raviaw/roundtftmonitor/stand/views/fit-dark.png

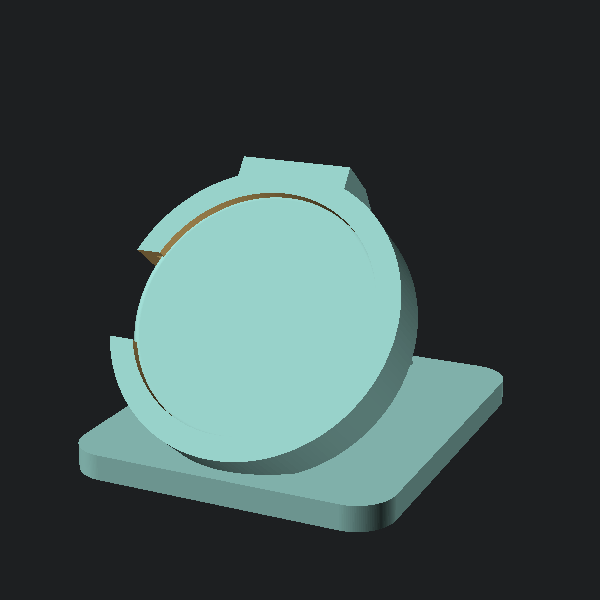
stand/views/fit-dark.png
