raviaw/roundtftmonitor/stand/views/fit-light.png

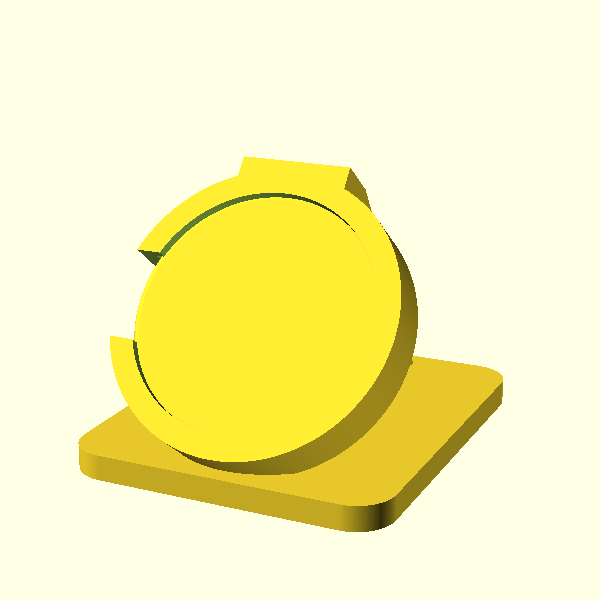
stand/views/fit-light.png
