raviaw/roundtftmonitor/stand/views/iso-dark.png

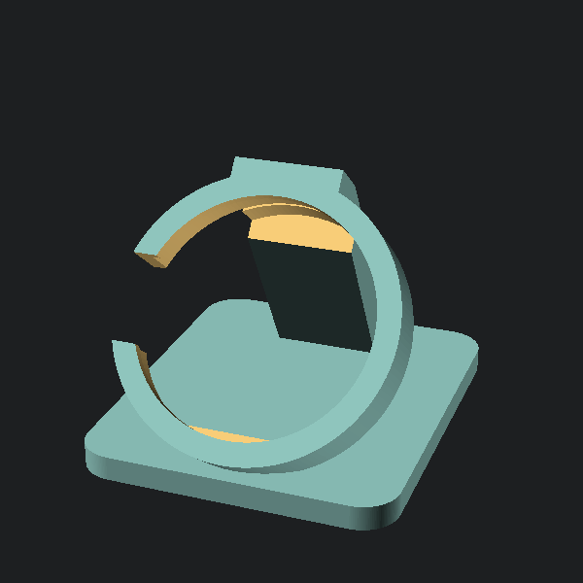
stand/views/iso-dark.png
