raviaw/roundtftmonitor/stand/views/top-light.png

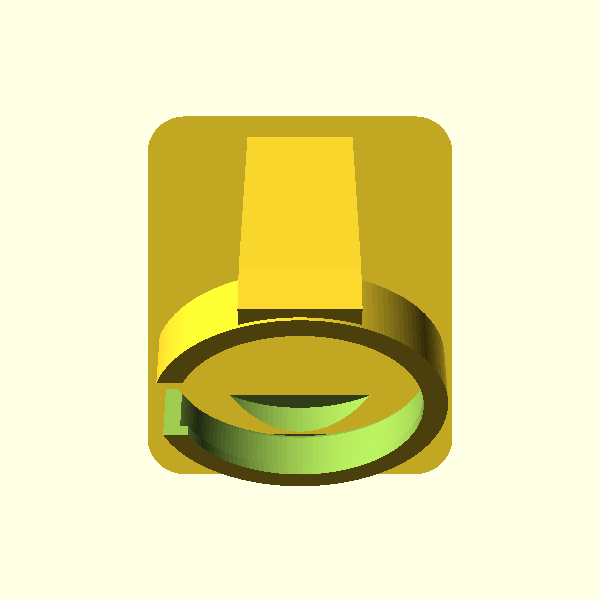
stand/views/top-light.png
