raviaw/roundtftmonitor/host/pc_monitor.py

#!/usr/bin/env python3
"""
Host agent for the roundtft PC + Claude monitor.

Streams to the ESP32-2424S012 over USB-serial, one line per update:
    cpu=37.5 ram=61.2 sess=26.0 week=56.0 usageage=42
    proc=chrome:8.43:12.5|Code:6.10:3.0|...      (top-7 by memory; <=7 items)

- usageage    : seconds since usage figures were last *successfully* fetched.
                Emitted only once there has been a success; lets the firmware gray
                out sess/week when the endpoint is failing (429/401) and the values
                have gone stale. Omitted entirely until the first success.

- cpu / ram  : PC CPU% and RAM% via psutil (no driver, no admin)
- sess / week: Claude Code 5-hour session% and 7-day week% from the (UNDOCUMENTED)
               OAuth usage endpoint, using the token Claude Code already stores
               in ~/.claude/.credentials.json. Refreshed at most once per minute.
- proc       : top-7 processes by memory as name:memGB:cpu items, '|'-separated.
               memGB = working set in GiB; cpu = share of the whole machine (%).
               One NtQuerySystemInformation call snapshots all processes (~7 ms,
               ~0 CPU); psutil is the per-pid fallback (~1 s) if that ever fails.
               Runs on a background thread so a scan never blocks the per-second
               CPU/RAM stream.

Deps: pyserial, psutil   (pip install pyserial psutil)  -- usage uses stdlib only.
Run:  python pc_monitor.py            # auto-detects the board's COM port
      python pc_monitor.py COM5       # or force a port
"""
import json
import os
import sys
import threading
import time
import urllib.error
import urllib.request
from datetime import datetime, timezone

# The autostart task launches pythonw.exe directly (no PYTHONPATH), so make the
# custom pip target importable here (override with ROUNDTFT_PIP). No-op if the
# packages are already importable / already on sys.path.
_PIP = os.environ.get("ROUNDTFT_PIP", r"E:\dev\pip")
if _PIP and os.path.isdir(_PIP) and _PIP not in sys.path:
    sys.path.insert(0, _PIP)

import psutil
import serial
from serial.tools import list_ports

# --- Fast top-process scan via the native process snapshot -------------------
# One NtQuerySystemInformation(SystemProcessInformation) call returns name,
# working-set memory, and CPU times for EVERY process in a single syscall (~7 ms,
# ~0 CPU). The psutil path needs an OpenProcess per pid instead (~900 ms, ~1 core
# of kernel time). We use this when it loads cleanly and fall back to psutil if
# the (undocumented) struct ever fails to line up on some Windows build.
try:
    import ctypes

    _ntdll = ctypes.WinDLL("ntdll")

    class _UNICODE_STRING(ctypes.Structure):
        _fields_ = [("Length", ctypes.c_ushort),
                    ("MaximumLength", ctypes.c_ushort),
                    ("Buffer", ctypes.c_void_p)]

    class _SPI(ctypes.Structure):           # SYSTEM_PROCESS_INFORMATION (x64)
        _fields_ = [
            ("NextEntryOffset", ctypes.c_ulong),
            ("NumberOfThreads", ctypes.c_ulong),
            ("WorkingSetPrivateSize", ctypes.c_longlong),
            ("HardFaultCount", ctypes.c_ulong),
            ("NumberOfThreadsHighWatermark", ctypes.c_ulong),
            ("CycleTime", ctypes.c_ulonglong),
            ("CreateTime", ctypes.c_longlong),
            ("UserTime", ctypes.c_longlong),        # 100 ns units, cumulative
            ("KernelTime", ctypes.c_longlong),      # 100 ns units, cumulative
            ("ImageName", _UNICODE_STRING),
            ("BasePriority", ctypes.c_long),
            ("UniqueProcessId", ctypes.c_void_p),
            ("InheritedFromUniqueProcessId", ctypes.c_void_p),
            ("HandleCount", ctypes.c_ulong),
            ("SessionId", ctypes.c_ulong),
            ("UniqueProcessKey", ctypes.c_size_t),
            ("PeakVirtualSize", ctypes.c_size_t),
            ("VirtualSize", ctypes.c_size_t),
            ("PageFaultCount", ctypes.c_ulong),
            ("PeakWorkingSetSize", ctypes.c_size_t),
            ("WorkingSetSize", ctypes.c_size_t),    # bytes; matches psutil rss
        ]

    _NtQSI = _ntdll.NtQuerySystemInformation
    _NtQSI.restype = ctypes.c_ulong
    _NtQSI.argtypes = [ctypes.c_ulong, ctypes.c_void_p, ctypes.c_ulong,
                       ctypes.POINTER(ctypes.c_ulong)]
    _SYSTEM_PROCESS_INFORMATION = 5
    _STATUS_INFO_LEN_MISMATCH = 0xC0000004
    _HAVE_NT = True
except Exception:
    _HAVE_NT = False

ESP_VID = 0x303A
ESP_PID = 0x1001
BAUD = 115200
INTERVAL = 1.0          # seconds between updates (also the CPU sample window)
PROC_REFRESH = 2.0      # seconds between scans on the fast (ctypes) path
PROC_REFRESH_SLOW = 15.0  # back off to this if we fall back to the psutil path
PROC_COUNT = 7          # how many processes the bars view shows
_NCPU = psutil.cpu_count() or 1
# Latest top-process list, published by the background scanner thread. Replacing
# the whole list is atomic under the GIL, so the main loop reads it lock-free.
_proc_items: list = []

# Are we attached to a real console? Under the autostart task we run as pythonw.exe
# with no console, so sys.stdout is None -> _TTY is False. In that case capture the
# connect/error lines in a small logfile (the per-second data line stays suppressed
# below, so it never grows unbounded). Interactive runs print live and write no file.
_TTY = bool(getattr(sys.stdout, "isatty", lambda: False)())
if not _TTY:
    try:
        _logdir = os.environ.get("LOCALAPPDATA") or os.path.expanduser("~")
        sys.stdout = sys.stderr = open(
            os.path.join(_logdir, "roundtft-monitor.log"), "a", buffering=1, encoding="utf-8")
    except Exception:
        pass


def _log(msg: str) -> None:
    """Timestamped event line (local time). Used for connect/disconnect/error
    events -- NOT the per-second data line -- so the log stays diagnosable."""
    print(f"{datetime.now().strftime('%Y-%m-%d %H:%M:%S')}  {msg}", flush=True)

# --- Claude usage (undocumented endpoint; may change/break without notice) ---
CRED_PATH = os.path.expanduser("~/.claude/.credentials.json")
USAGE_URL = "https://api.anthropic.com/api/oauth/usage"
# Poll gently and back off hard: bursting (the old 30s retry) trips a 429 with
# Retry-After 300. The firmware grays stale values via usageage=, so a slow refresh is
# harmless. NB most of the 429 storms we chased were really this endpoint throttling
# *dead-token* retries -- fix the token (below) and they stop.
USAGE_REFRESH = 900.0   # seconds; re-query after a *successful* fetch (15 min)
USAGE_FAIL_BACKOFF = 300.0  # seconds; gentle wait after a 429/other failure
USAGE_RETRY_MAX = 900.0  # cap on any server-supplied Retry-After backoff
USAGE_TOKEN_POLL = 30.0  # seconds; cheap creds-file re-read cadence (no network)
                         # while the token is missing or a 401'd token awaits rotation
USAGE_401_MAX_WAIT = 900.0  # re-probe the network at most this often while a 401'd
                            # token persists unchanged (fluke-recovery safety net)
SESSION_PERIOD = 5 * 3600        # 5-hour rolling window
WEEK_PERIOD = 7 * 24 * 3600      # nominal 7-day window (tune if it resets sooner)

# --- OAuth token self-refresh ------------------------------------------------
# accessToken lives ~8 h and only Claude Code ever refreshed it, so a day without
# Claude Code left us 401ing (and then 429ing, as the endpoint throttles dead-token
# retries) until the user next opened it. We run the standard refresh_token grant
# ourselves, against the same endpoint and client id Claude Code uses, so usage
# survives with Claude Code closed -- now bounded by refreshTokenExpiresAt (~9 days)
# rather than 8 hours.
# Host choice: api.anthropic.com, same as USAGE_URL. platform.claude.com sits behind a
# Cloudflare rule that 403s (error 1010) urllib's default User-Agent, and
# console.anthropic.com now 404s. We send a real UA regardless, so we don't depend on
# api.anthropic.com staying exempt from that rule.
OAUTH_TOKEN_URL = "https://api.anthropic.com/v1/oauth/token"
OAUTH_CLIENT_ID = "9d1c250a-e61b-44d9-88ed-5944d1962f5e"  # Claude Code's public client
OAUTH_UA = "claude-cli/2.0.14 (external, cli)"
REFRESH_SKEW = 600.0     # refresh once the accessToken has under 10 min of life left
CRED_ACTIVE_WINDOW = 120.0  # creds written this recently => Claude Code is live and
                            # rotating them itself; use its token, don't race its refresh
REFRESH_MIN_INTERVAL = 60.0  # floor between our own refresh attempts (never hammer)
# "next": monotonic time before which get_claude_usage() serves the cache without
# hitting the network. Advanced by USAGE_REFRESH on success, USAGE_FAIL_BACKOFF (or
# the 429 Retry-After) on failure. "bad_token": an accessToken a 401 proved dead -- we
# refresh it ourselves, and only fall back to serving cache (cheap file reads only) if
# that's impossible. "refresh_at": last refresh attempt, throttled by
# REFRESH_MIN_INTERVAL.
_usage = {"sess": None, "week": None, "sessp": None, "weekp": None,
          "sessh": None, "weekh": None, "next": 0.0, "ok_at": None, "fails": 0,
          "bad_token": None, "bad_at": 0.0, "refresh_at": -REFRESH_MIN_INTERVAL}


def _remaining_seconds(resets_at):
    if not resets_at:
        return None
    try:
        reset = datetime.fromisoformat(resets_at)
        return max(0.0, (reset - datetime.now(timezone.utc)).total_seconds())
    except Exception:
        return None


def _period_progress(resets_at, period_sec):
    """Fraction (0..100) of the window already elapsed: 100 = about to reset."""
    rem = _remaining_seconds(resets_at)
    return None if rem is None else max(0.0, min(100.0, (1.0 - rem / period_sec) * 100.0))


def _hours_left(resets_at):
    rem = _remaining_seconds(resets_at)
    return None if rem is None else rem / 3600.0


def find_port() -> str | None:
    for p in list_ports.comports():
        if p.vid == ESP_VID and p.pid == ESP_PID:
            return p.device
    return None


def _read_creds() -> dict | None:
    """The whole claudeAiOauth blob (accessToken/refreshToken/expiresAt), or None."""
    try:
        with open(CRED_PATH, encoding="utf-8") as fh:
            return json.load(fh)["claudeAiOauth"]
    except Exception:
        return None


def _creds_age() -> float:
    """Seconds since .credentials.json was last written; inf if unreadable. Fresh =>
    Claude Code is running and refreshing the token itself."""
    try:
        return max(0.0, time.time() - os.path.getmtime(CRED_PATH))
    except OSError:
        return float("inf")


def _expires_in(creds: dict) -> float | None:
    """Seconds of accessToken life left (negative = already expired); None if absent."""
    exp = creds.get("expiresAt")
    if not isinstance(exp, (int, float)):
        return None
    return exp / 1000.0 - time.time()   # expiresAt is epoch MILLIseconds


def _save_creds(updates: dict) -> None:
    """Merge `updates` into claudeAiOauth and replace the file atomically, keeping a
    .bak of the previous contents. Re-reads immediately before writing so we preserve
    any field (and any concurrent Claude Code edit) we don't own."""
    with open(CRED_PATH, encoding="utf-8") as fh:
        blob = json.load(fh)
    try:
        with open(CRED_PATH + ".bak", "w", encoding="utf-8") as fh:
            json.dump(blob, fh, indent=2)
    except OSError as e:
        _log(f"credentials backup failed (continuing): {e}")
    blob.setdefault("claudeAiOauth", {}).update(updates)
    tmp = CRED_PATH + ".tmp"
    with open(tmp, "w", encoding="utf-8") as fh:
        json.dump(blob, fh, indent=2)
    os.replace(tmp, CRED_PATH)   # atomic: readers see old or new, never a partial file


def _refresh_access_token(creds: dict) -> str | None:
    """OAuth refresh_token grant -> new accessToken, persisted for Claude Code to pick
    up. The refresh token rotates, so writing the new one back is mandatory: dropping it
    would strand Claude Code on a spent token. Returns the new access token, or None."""
    rt = creds.get("refreshToken")
    if not rt:
        return None
    body = json.dumps({
        "grant_type": "refresh_token",
        "refresh_token": rt,
        "client_id": OAUTH_CLIENT_ID,
    }).encode()
    req = urllib.request.Request(OAUTH_TOKEN_URL, data=body, method="POST", headers={
        "Content-Type": "application/json",
        "Accept": "application/json",
        "User-Agent": OAUTH_UA,
    })
    try:
        with urllib.request.urlopen(req, timeout=15) as resp:
            data = json.load(resp)
    except urllib.error.HTTPError as e:
        # A rejected grant is usually benign: Claude Code rotated this same refresh token
        # between our read and our POST, so the token we sent was already spent. Its
        # replacement is on disk already -- adopt that instead of crying "log in again".
        if e.code in (400, 401):
            current = _read_creds() or {}
            if current.get("refreshToken") not in (None, rt):
                _log("refresh raced Claude Code's own rotation; adopting its token")
                return current.get("accessToken")
        raise
    at = data.get("access_token")
    if not at:
        return None
    updates = {"accessToken": at}
    if data.get("refresh_token"):        # rotated -> persist or Claude Code is stranded
        updates["refreshToken"] = data["refresh_token"]
    if data.get("expires_in"):
        updates["expiresAt"] = int((time.time() + float(data["expires_in"])) * 1000)
    if data.get("scope"):
        updates["scopes"] = data["scope"].split()
    _save_creds(updates)
    return at


def _fresh_token() -> str | None:
    """accessToken with life left in it: refresh it ourselves when it's near expiry and
    Claude Code isn't around to do it. Never raises -- falls back to whatever's on disk."""
    creds = _read_creds()
    if not creds:
        return None
    token = creds.get("accessToken")
    left = _expires_in(creds)
    if left is None or left > REFRESH_SKEW:
        return token                      # still good; nothing to do
    idle = _creds_age()
    if idle < CRED_ACTIVE_WINDOW:
        return token                      # Claude Code just wrote these -- let it drive
    now = time.monotonic()
    if now - _usage["refresh_at"] < REFRESH_MIN_INTERVAL:
        return token
    _usage["refresh_at"] = now
    try:
        new = _refresh_access_token(creds)
    except urllib.error.HTTPError as e:
        # 400/401 here = the refresh token itself is spent or revoked; only a real
        # `claude` login can fix that, so say so instead of retrying forever.
        detail = "refresh token rejected -- run `claude` to sign in again" \
            if e.code in (400, 401) else f"retry in {REFRESH_MIN_INTERVAL:.0f}s"
        _log(f"token refresh failed: {e}; {detail}")
        return token
    except Exception as e:
        _log(f"token refresh failed: {e}; retry in {REFRESH_MIN_INTERVAL:.0f}s")
        return token
    if new:
        state = f"expired {-left / 60:.0f} min ago" if left < 0 else f"{left / 60:.0f} min left"
        _log(f"refreshed accessToken ({state}; Claude Code idle {idle / 3600:.1f} h)")
        return new
    return token


def _retry_after(err, default):
    """Seconds to wait per an HTTP 429's Retry-After header, capped; else default."""
    try:
        ra = err.headers.get("Retry-After")
        if ra is not None:
            return max(USAGE_FAIL_BACKOFF, min(USAGE_RETRY_MAX, float(ra)))
    except Exception:
        pass
    return default


def _force_refresh() -> str | None:
    """Refresh regardless of expiresAt -- for when the server 401s a token that still
    looked live on paper (clock skew, or a token revoked early). Throttled the same way."""
    creds = _read_creds()
    if not creds or _creds_age() < CRED_ACTIVE_WINDOW:
        return None                      # Claude Code is live; its next write wins
    now = time.monotonic()
    if now - _usage["refresh_at"] < REFRESH_MIN_INTERVAL:
        return None
    _usage["refresh_at"] = now
    try:
        new = _refresh_access_token(creds)
    except urllib.error.HTTPError as e:
        detail = "refresh token rejected -- run `claude` to sign in again" \
            if e.code in (400, 401) else "will retry"
        _log(f"token refresh failed: {e}; {detail}")
        return None
    except Exception as e:
        _log(f"token refresh failed: {e}; will retry")
        return None
    if new:
        _log("refreshed accessToken after a 401")
    return new


def get_claude_usage() -> dict:
    """Usage % + period-progress % from the OAuth endpoint. Serves a cache until
    _usage["next"]: USAGE_REFRESH after a success, USAGE_FAIL_BACKOFF (or the 429
    Retry-After) after a failure, and -- after a 401 -- cheap file re-reads only
    until Claude Code rotates the token, so we never burst past the endpoint's
    tight shared rate limit. Keeps last known values (or None) on failure -- never
    raises."""
    now = time.monotonic()
    if now < _usage["next"]:
        return _usage

    token = _fresh_token()  # re-read each time, and refresh it ourselves if it's stale
    if not token:
        _usage["next"] = now + USAGE_TOKEN_POLL   # creds not ready yet -- look again soon
        return _usage
    # A 401 proved this exact token dead. Don't hit the network again until Claude
    # Code rotates accessToken (cheap file re-reads only); re-probe at most every
    # USAGE_401_MAX_WAIT in case the 401 was a fluke.
    if token == _usage["bad_token"] and (now - _usage["bad_at"]) < USAGE_401_MAX_WAIT:
        _usage["next"] = now + USAGE_TOKEN_POLL
        return _usage

    req = urllib.request.Request(USAGE_URL, headers={
        "Authorization": f"Bearer {token}",
        "anthropic-beta": "oauth-2025-04-20",
        "anthropic-version": "2023-06-01",
        "Accept": "application/json",
    })
    try:
        with urllib.request.urlopen(req, timeout=10) as resp:
            data = json.load(resp)
        fh = data.get("five_hour") or {}
        sd = data.get("seven_day") or {}
        _usage["sess"]  = fh.get("utilization")
        _usage["week"]  = sd.get("utilization")
        _usage["sessp"] = _period_progress(fh.get("resets_at"), SESSION_PERIOD)
        _usage["weekp"] = _period_progress(sd.get("resets_at"), WEEK_PERIOD)
        _usage["sessh"] = _hours_left(fh.get("resets_at"))
        _usage["weekh"] = _hours_left(sd.get("resets_at"))
        _usage["next"] = now + USAGE_REFRESH
        _usage["ok_at"] = now       # last *successful* fetch -> feeds usageage= (staleness)
        _usage["bad_token"] = None  # this token works -> clear any 401 rotation-wait
        if _usage["fails"]:         # log recovery once (mirrors the board "was absent Ns" line)
            _log(f"usage fetch OK (sess={_usage['sess']} week={_usage['week']}) "
                 f"after {_usage['fails']} failures")
            _usage["fails"] = 0
    except urllib.error.HTTPError as e:
        if e.code == 401:
            # This exact token is dead. Refresh it ourselves right now; only if that
            # can't be done (Claude Code mid-rotation, refresh throttled, or the refresh
            # token itself is spent) do we fall back to waiting for Claude Code to
            # rewrite it -- cheap file reads, never a network burst, which is what
            # tripped the 429s.
            _usage["bad_token"] = token
            _usage["bad_at"] = now
            if _force_refresh():
                _usage["next"] = now       # new token in hand -> retry on the next tick
            else:
                _usage["next"] = now + USAGE_TOKEN_POLL
                _log(f"usage fetch failed: {e}; awaiting token rotation")
        else:
            # 429 = rate-limited (respect Retry-After); back off gently.
            wait = _retry_after(e, USAGE_FAIL_BACKOFF) if e.code == 429 else USAGE_FAIL_BACKOFF
            _usage["next"] = now + wait
            _log(f"usage fetch failed: {e}; retry in {wait:.0f}s")
        _usage["fails"] += 1
    except Exception as e:
        _log(f"usage fetch failed: {e}; retry in {USAGE_FAIL_BACKOFF:.0f}s")
        _usage["next"] = now + USAGE_FAIL_BACKOFF
        _usage["fails"] += 1
    return _usage


def _san(name: str) -> str:
    """Trim a process name for the display: drop the .exe, strip the field
    delimiters (':' '|') and any non-printable bytes, cap at 12 chars."""
    if name.lower().endswith(".exe"):
        name = name[:-4]
    name = "".join(c for c in name if 32 < ord(c) < 127 and c not in ":|")
    return name[:12] or "?"


_TOTAL_RAM = psutil.virtual_memory().total
_BYTES_PER_GB = 1073741824.0  # GiB -- what Windows labels "GB"
_TOTAL_GB = _TOTAL_RAM / _BYTES_PER_GB
_prev_cpu: dict = {}        # pid -> cumulative (user+kernel) CPU, 100 ns units
_prev_cpu_ts = 0.0          # monotonic time of the previous fast scan


def _scan_fast() -> list:
    """Top PROC_COUNT by memory via one NtQuerySystemInformation call (~7 ms,
    ~0 CPU). memGB = working set in GiB; cpu% = share of the whole machine,
    derived from the user+kernel CPU-time delta since the previous scan (so the
    first scan reads 0 until there are two points to diff)."""
    global _prev_cpu, _prev_cpu_ts
    size = 512 * 1024
    while True:
        buf = (ctypes.c_byte * size)()
        need = ctypes.c_ulong(0)
        st = _NtQSI(_SYSTEM_PROCESS_INFORMATION, buf, size, ctypes.byref(need))
        if st == 0:
            break
        if st == _STATUS_INFO_LEN_MISMATCH:        # snapshot grew; enlarge + retry
            size = max(need.value + 65536, size * 2)
            continue
        raise OSError(f"NtQuerySystemInformation -> {st:#010x}")

    now = time.monotonic()
    dt = (now - _prev_cpu_ts) if _prev_cpu_ts else 0.0
    base, off = ctypes.addressof(buf), 0
    cur_cpu, rows = {}, []
    while True:
        spi = _SPI.from_address(base + off)
        ws = spi.WorkingSetSize
        if ws > 0:
            pid = spi.UniqueProcessId or 0
            if spi.ImageName.Buffer and spi.ImageName.Length:
                name = ctypes.wstring_at(spi.ImageName.Buffer, spi.ImageName.Length // 2)
            else:
                name = "?"
            cput = spi.UserTime + spi.KernelTime          # 100 ns units, cumulative
            cur_cpu[pid] = cput
            cpu = 0.0
            if dt > 0:
                prev = _prev_cpu.get(pid)
                if prev is not None:
                    cpu = max(0.0, (cput - prev) / 1e7 / (dt * _NCPU) * 100.0)
            rows.append((_san(name), ws / _BYTES_PER_GB, cpu))   # memory in GiB
        if spi.NextEntryOffset == 0:
            break
        off += spi.NextEntryOffset

    _prev_cpu, _prev_cpu_ts = cur_cpu, now
    rows.sort(key=lambda r: r[1], reverse=True)
    return rows[:PROC_COUNT]


def _scan_psutil() -> list:
    """Fallback: top PROC_COUNT by memory via psutil. Correct everywhere but
    costs an OpenProcess per pid (~1 s, ~1 core of kernel time on a busy box),
    so the scanner backs off to PROC_REFRESH_SLOW when it has to use this."""
    rows = []
    # process_iter caches Process objects across calls, so cpu_percent() returns
    # a proper delta over the refresh interval; ['attrs'] batches via oneshot().
    for p in psutil.process_iter(["name", "memory_percent", "cpu_percent"]):
        try:
            info = p.info
            mem = info.get("memory_percent") or 0.0
            if mem <= 0.0:
                continue
            cpu = (info.get("cpu_percent") or 0.0) / _NCPU
            memgb = mem / 100.0 * _TOTAL_GB
            rows.append((_san(info.get("name") or "?"), memgb, cpu))
        except (psutil.NoSuchProcess, psutil.AccessDenied):
            continue
    rows.sort(key=lambda r: r[1], reverse=True)
    return rows[:PROC_COUNT]


def _proc_scanner() -> None:
    """Background loop publishing the latest top-process list. Uses the fast
    native scan; if that ever raises (struct mismatch on some Windows build) it
    latches onto the psutil fallback for the rest of the run. Off the main loop
    either way, so a scan never stalls the per-second CPU/RAM/usage stream.
    Daemon thread -- dies with the process."""
    global _proc_items
    use_nt = _HAVE_NT
    while True:
        slow = not use_nt
        try:
            _proc_items = _scan_fast() if use_nt else _scan_psutil()
        except Exception as e:
            if use_nt:
                _log(f"fast proc scan failed ({e}); falling back to psutil")
                use_nt = False
            try:
                _proc_items = _scan_psutil()
                slow = True
            except Exception as e2:
                _log(f"proc scan failed: {e2}")
        time.sleep(PROC_REFRESH_SLOW if slow else PROC_REFRESH)


def build_line() -> str:
    cpu = psutil.cpu_percent(interval=INTERVAL)   # blocks INTERVAL secs; paces the loop
    ram = psutil.virtual_memory().percent
    parts = [f"cpu={cpu:.1f}", f"ram={ram:.1f}"]
    u = get_claude_usage()
    for key in ("sess", "week", "sessp", "weekp", "sessh", "weekh"):
        if u[key] is not None:
            parts.append(f"{key}={u[key]:.1f}")
    # Age of the usage figures so the firmware can gray them when they go stale
    # (the 429/401-storm case: cached values keep streaming, but stop being fresh).
    if u["ok_at"] is not None:
        parts.append(f"usageage={int(time.monotonic() - u['ok_at'])}")
    line = " ".join(parts) + "\n"
    procs = _proc_items                       # snapshot the latest scan (lock-free)
    if procs:
        line += "proc=" + "|".join(f"{n}:{m:.2f}:{c:.1f}" for n, m, c in procs) + "\n"
    return line


def main() -> None:
    forced = sys.argv[1] if len(sys.argv) > 1 else None
    psutil.cpu_percent()   # prime the CPU counter
    threading.Thread(target=_proc_scanner, daemon=True).start()  # top-procs, off the hot path

    ser = None
    missing_since = None          # monotonic time the board first went absent (None = present)
    while True:
        try:
            if ser is None or not ser.is_open:
                port = forced or find_port()
                if not port:
                    if missing_since is None:      # log the outage once, not every 2 s
                        missing_since = time.monotonic()
                        _log("board not found (303A:1001); retrying every 2 s...")
                    time.sleep(2)
                    continue
                ser = serial.Serial(port, BAUD, timeout=1)
                if missing_since is not None:
                    gone = time.monotonic() - missing_since
                    _log(f"connected on {port} (was absent {gone:.0f} s)")
                    missing_since = None
                else:
                    _log(f"connected on {port}")

            line = build_line()
            ser.write(line.encode("ascii"))
            if _TTY:
                print(line.strip(), flush=True)
        except (serial.SerialException, OSError) as e:
            _log(f"serial error: {e}; reconnecting...")
            try:
                if ser:
                    ser.close()
            except Exception:
                pass
            ser = None
            time.sleep(2)
        except KeyboardInterrupt:
            print("\nstopping", flush=True)
            break


if __name__ == "__main__":
    main()
